sean-galloway/RaspberyPi-IMSAI-8080/firmware/src/crc8.c

#include "crc8.h"

uint8_t crc8(const uint8_t *data, size_t len) {
    uint8_t crc = 0x00;
    for (size_t i = 0; i < len; i++) {
        crc ^= data[i];
        for (int b = 0; b < 8; b++) {
            crc = (crc & 0x80) ? (uint8_t)((crc << 1) ^ 0x07)
                               : (uint8_t)(crc << 1);
        }
    }
    return crc;
}
